mcbearfish/Mini-3D-Window-Viewer/ARviewercode/Core/Src/Sensors/magneto.h

/**
  ******************************************************************************
  * @file    magneto.h
  * @author  MCD Application Team
  * @version V4.0.1
  * @date    21-July-2015
  * @brief   This header file contains the functions prototypes for the MAGNETO driver.
  ******************************************************************************
  * @attention
  *
  * <h2><center>&copy; COPYRIGHT(c) 2015 STMicroelectronics</center></h2>
  *
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
  ******************************************************************************
  */

/* Define to prevent recursive inclusion -------------------------------------*/
#ifndef __MAGNETO_H
#define __MAGNETO_H

#ifdef __cplusplus
 extern "C" {
#endif

/* Includes ------------------------------------------------------------------*/
#include <stdint.h>

/** @addtogroup BSP
  * @{
  */

/** @addtogroup Components
  * @{
  */

/** @addtogroup MAGNETO
  * @{
  */

/** @defgroup MAGNETO_Exported_Types
  * @{
  */

/** @defgroup MAGNETO_Config_structure  Magnetometer Configuration structure
  * @{
  */
typedef struct
{
  uint8_t Register1;
  uint8_t Register2;
  uint8_t Register3;
  uint8_t Register4;
  uint8_t Register5;
}MAGNETO_InitTypeDef;
/**
  * @}
  */

/** @defgroup MAGNETO_Driver_structure  Magnetometer Driver structure
  * @{
  */
typedef struct
{
  void      (*Init)(MAGNETO_InitTypeDef);
  void      (*DeInit)(void);
  uint8_t   (*ReadID)(void);
  void      (*Reset)(void);
  void      (*LowPower)(void);
  void      (*ConfigIT)(void);
  void      (*EnableIT)(uint8_t);
  void      (*DisableIT)(uint8_t);
  uint8_t   (*ITStatus)(uint16_t);
  void      (*ClearIT)(void);
  void      (*FilterConfig)(uint8_t);
  void      (*FilterCmd)(uint8_t);
  void      (*GetXYZ)(int16_t *);
}MAGNETO_DrvTypeDef;
/**
  * @}
  */

/**
  * @}
  */

/**
  * @}
  */

/**
  * @}
  */

/**
  * @}
  */

#ifdef __cplusplus
}
#endif

#endif /* __MAGNETO_H */

/************************ (C) COPYRIGHT STMicroelectronics *****END OF FILE****/
